24849748/exS3-mix/Pictures/3.jpg

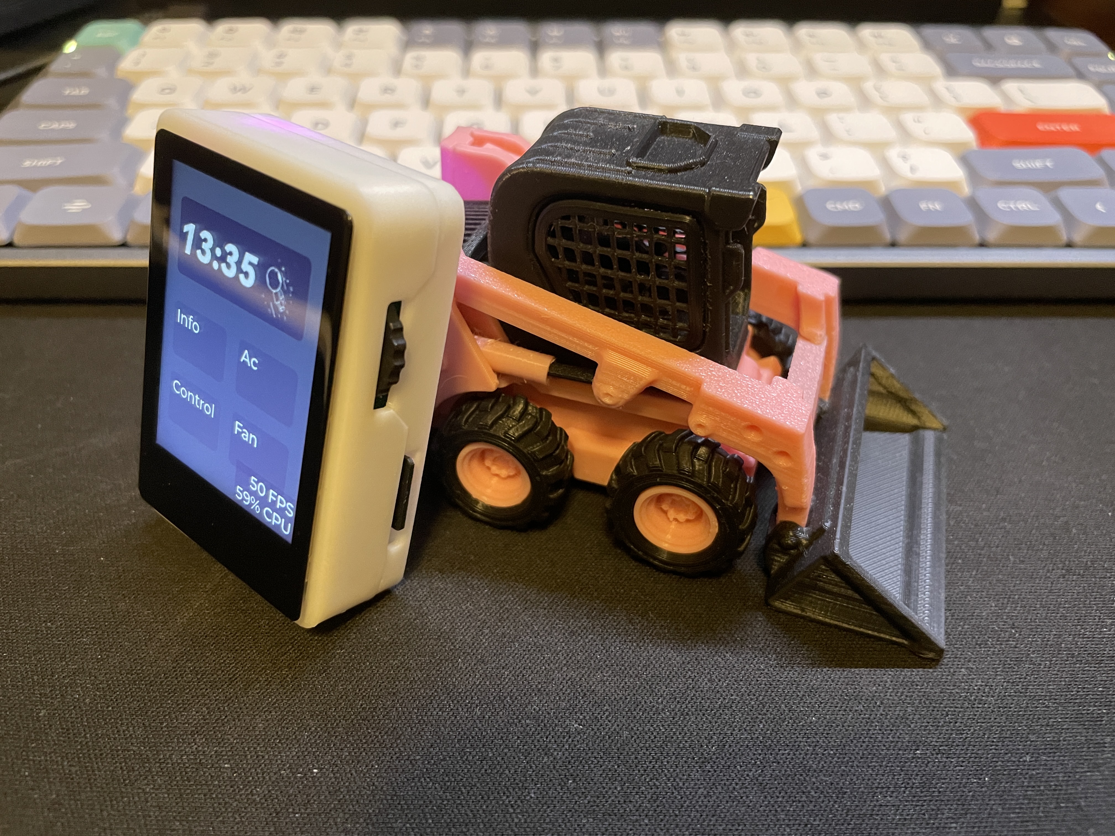
Pictures/3.jpg
